m0xpd/SubHarmonics/Hardware/SubHarmonics Main Board v2.sch

## EAGLE design Hardware/SubHarmonics Main Board v2.sch (2023-10-22, an earlier design)

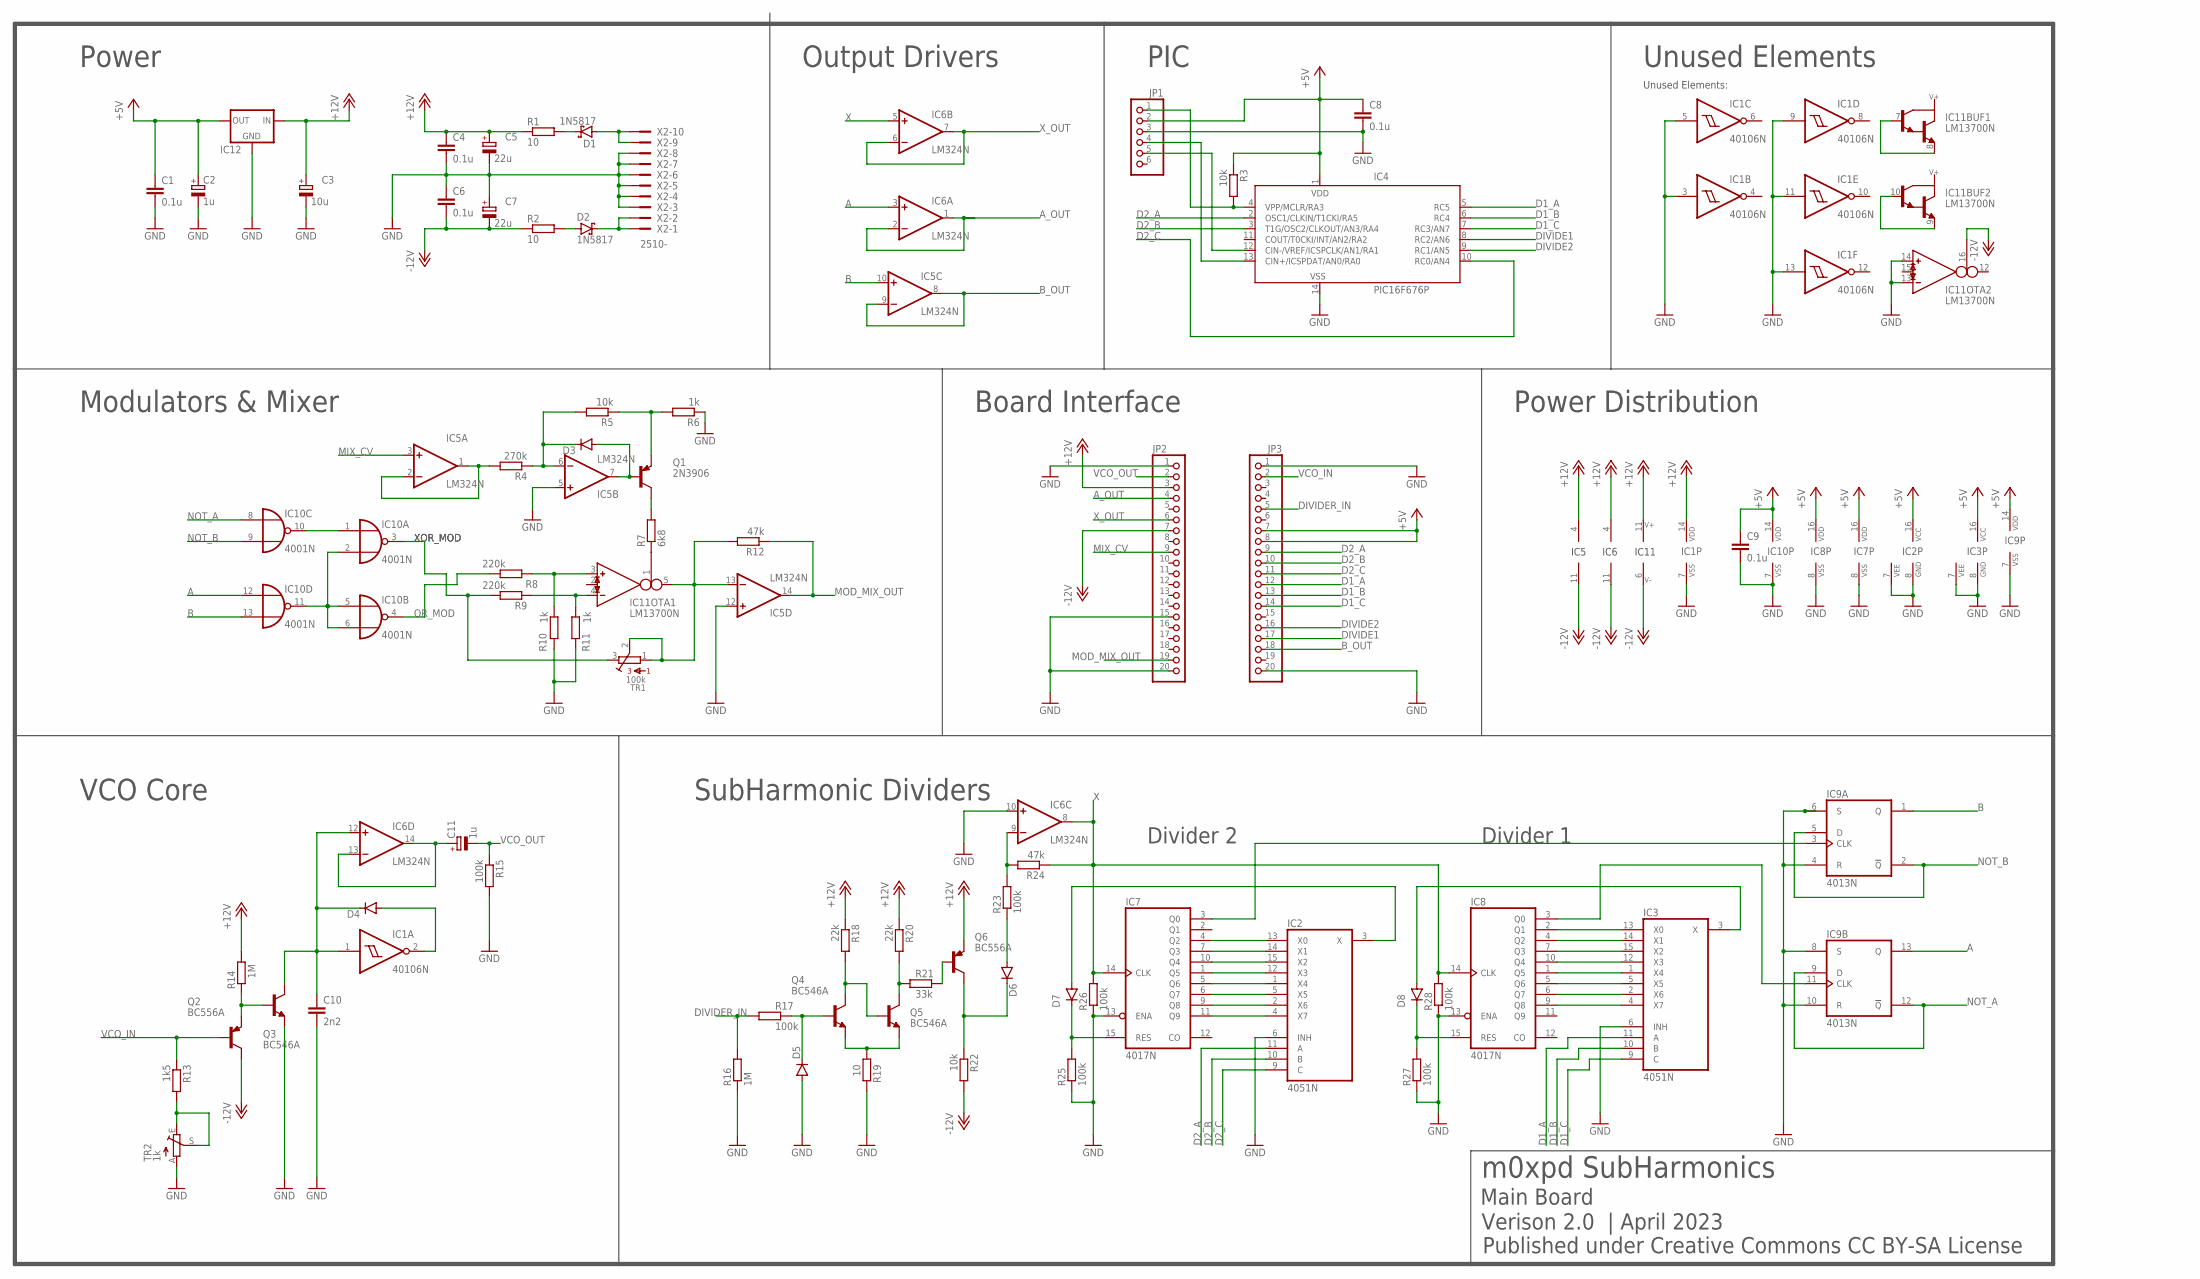
[picture p9: schematic SubHarmonics Main Board v2.sch]

Parts:
C1, C4, C6, C8, C9: 0.1u; C050-025X075
C2, C11: 1u; E2,5-5
C3: 10u; E2,5-5
C5, C7: 22u; E2,5-5
C10: 2n2; C050-030X075
D1, D2: 1N5817; DO35-7
D3, D4, D5, D6, D7, D8: 1N4148DO35-7; DO35-7
IC1: 40106N; DIL14
IC2, IC3: 4051N; DIL16
IC4: PIC16F676P; DIL14
IC5, IC6: LM324N; DIL14
IC7, IC8: 4017N; DIL16
IC9: 4013N; DIL14
IC10: 4001N; DIL14
IC11: LM13700N; DIL16
IC12: 78LXX
JP1: PINHD-1X6; 1X06
JP2, JP3: PINHD-1X20; 1X20
Q1: 2N3906; TO92
Q2, Q6: BC556A; TO92-EBC
Q3, Q4, Q5: BC546A; TO92-EBC
R1, R2, R19: 10; 0204/7
R3, R5, R22: 10k; 0204/7
R4: 270k; 0204/7
R6, R10, R11: 1k; 0204/7
R7: 6k8; 0204/7
R8, R9: 220k; 0204/7
R12, R24: 47k; 0204/7
R13: 1k5; 0204/7
R14, R16: 1M; 0204/7
R15, R17, R23, R25, R26, R27, R28: 100k; 0204/7
R18, R20: 22k; 0204/7
R21: 33k; 0204/7
TR1: 100k; BOURNS_3362P_TRIMMER
TR2: 1k; B64Y
X2: 2510-; PAK100/2500-10

Connections:
+5V: C1.1, C2.+, C8.1, C9.1, IC2.16 (VCC), IC3.16 (VCC), IC4.1 (VDD), IC7.16 (VDD), IC8.16 (VDD), IC9.14 (VDD), IC10.14 (VDD), IC12.OUT, JP1.2, JP3.7, JP3.8, R3.1
+12V: C3.+, C4.1, C5.+, IC1.14 (VDD), IC5.4 (V+), IC6.4 (V+), IC11.11 (V+), IC12.IN, JP2.3, Q6.E, R1.1, R14.2, R18.1, R20.1
-12V: C6.2, C7.-, IC5.11 (V-), IC6.11 (V-), IC11.6 (V-), IC11.16 (I_BIAS), JP2.7, Q2.C, R2.1, R22.2
A: IC6.3 (+IN), IC9.13 (Q), IC10.12 (I0)
A_OUT: IC6.1 (OUT), IC6.2 (-IN), JP2.4
B: IC5.10 (+IN), IC9.1 (Q), IC10.13 (I1)
B_OUT: IC5.8 (OUT), IC5.9 (-IN), JP3.18
D1_A: IC3.11 (A), IC4.5 (RC5), JP3.12
D1_B: IC3.10 (B), IC4.6 (RC4), JP3.13
D1_C: IC3.9 (C), IC4.7 (RC3/AN7), JP3.14
D2_A: IC2.11 (A), IC4.2 (OSC1/CLKIN/T1CKI/RA5), JP3.9
D2_B: IC2.10 (B), IC4.3 (T1G/OSC2/CLKOUT/AN3/RA4), JP3.10
D2_C: IC2.9 (C), IC4.10 (RC0/AN4), JP3.11
DIVIDE1: IC4.8 (RC2/AN6), JP3.17
DIVIDE2: IC4.9 (RC1/AN5), JP3.16
DIVIDER_IN: JP3.5, R16.2, R17.1
GND: C1.2, C2.-, C3.-, C4.2, C5.-, C6.1, C7.+, C8.2, C9.2, C10.2, D5.A, IC1.3 (I), IC1.5 (I), IC1.7 (VSS), IC1.9 (I), IC1.11 (I), IC1.13 (I), IC2.6 (INH), IC2.7 (VEE), IC2.8 (GND), IC3.6 (INH), IC3.7 (VEE), IC3.8 (GND), IC4.14 (VSS), IC5.5 (+IN), IC5.12 (+IN), IC6.10 (+IN), IC7.8 (VSS), IC7.13 (ENA), IC8.8 (VSS), IC8.13 (ENA), IC9.4 (R), IC9.6 (S), IC9.7 (VSS), IC9.8 (S), IC9.10 (R), IC10.7 (VSS), IC11.13 (IN_N), IC11.14 (IN_P), IC12.GND, JP1.3, JP2.1, JP2.15, JP2.20, JP3.1, JP3.20, Q3.E, R6.1, R10.2, R11.2, R15.2, R16.1, R19.2, R25.1, R26.1, R27.1, R28.1, TR2.A, X2.3, X2.4, X2.5, X2.6, X2.7, X2.8
MIX_CV: IC5.3 (+IN), JP2.9
MOD_MIX_OUT: IC5.14 (OUT), JP2.19, R12.1
unnamed: IC2.2 (X6), IC7.9 (Q8)
unnamed: IC5.1 (OUT), IC5.2 (-IN), R4.2
unnamed: D7.C, IC7.15 (RES), R25.2
unnamed: D7.A, IC2.3 (X)
unnamed: IC2.13 (X0), IC7.4 (Q2)
unnamed: IC2.14 (X1), IC7.7 (Q3)
unnamed: IC2.15 (X2), IC7.10 (Q4)
unnamed: IC2.12 (X3), IC7.1 (Q5)
unnamed: IC2.1 (X4), IC7.5 (Q6)
unnamed: IC2.5 (X5), IC7.6 (Q7)
unnamed: IC2.4 (X7), IC7.11 (Q9)
unnamed: IC11.3 (IN_P), R8.1, R10.1
unnamed: D1.A, X2.9, X2.10
unnamed: D1.C, R1.2
unnamed: IC4.4 (VPP/MCLR/RA3), JP1.1, R3.2
unnamed: D8.C, IC8.15 (RES), R27.2
unnamed: D8.A, IC3.3 (X)
unnamed: IC11.7 (B), IC11.8 (E)
unnamed: IC3.14 (X1), IC8.4 (Q2)
unnamed: IC3.15 (X2), IC8.7 (Q3)
unnamed: IC3.12 (X3), IC8.10 (Q4)
unnamed: IC3.1 (X4), IC8.1 (Q5)
unnamed: IC3.5 (X5), IC8.5 (Q6)
unnamed: IC3.2 (X6), IC8.6 (Q7)
unnamed: IC3.4 (X7), IC8.9 (Q8)
unnamed: IC11.4 (IN_N), R9.1, R11.1
unnamed: D2.A, R2.2
unnamed: D2.C, X2.1, X2.2
unnamed: IC11.9 (E), IC11.10 (B)
unnamed: IC11.1 (I_BIAS), R7.1
unnamed: IC4.13 (CIN+/ICSPDAT/AN0/RA0), JP1.4
unnamed: IC4.12 (CIN-/VREF/ICSPCLK/AN1/RA1), JP1.5
unnamed: IC3.13 (X0), IC8.2 (Q1)
unnamed: IC8.3 (Q0), IC9.11 (CLK)
unnamed: IC7.3 (Q0), IC9.3 (CLK)
unnamed: R13.2, TR2.E, TR2.S
unnamed: D6.C, Q6.C, R22.1
unnamed: D6.A, R23.1
unnamed: D4.A, IC1.2 (O)
unnamed: C10.1, D4.C, IC1.1 (I), IC6.12 (+IN), Q3.C
unnamed: Q2.E, Q3.B, R14.1
unnamed: IC6.9 (-IN), R23.2, R24.2
unnamed: C11.+, IC6.13 (-IN), IC6.14 (OUT)
unnamed: Q4.E, Q5.E, R19.1
unnamed: IC10.1 (I0), IC10.10 (O)
unnamed: IC10.2 (I1), IC10.5 (I0), IC10.6 (I1), IC10.11 (O)
unnamed: D5.C, Q4.B, R17.2
unnamed: Q1.1 (C), R7.2
unnamed: D3.C, IC5.6 (-IN), R4.1, R5.2
unnamed: Q4.C, Q5.B, R18.2
unnamed: Q5.C, R20.2, R21.1
unnamed: D3.A, IC5.7 (OUT), Q1.2 (B)
unnamed: Q1.3 (E), R5.1, R6.2
unnamed: Q6.B, R21.2
unnamed: IC5.13 (-IN), IC11.5 (OUT), R12.2, TR1.1, TR1.2
NOT_A: IC9.9 (D), IC9.12 (!Q), IC10.8 (I0)
NOT_B: IC9.2 (!Q), IC9.5 (D), IC10.9 (I1)
OR_MOD: IC10.4 (O), R8.2
VCO_IN: JP3.2, Q2.B, R13.1
VCO_OUT: C11.-, JP2.2, R15.1
X: IC6.5 (+IN), IC6.8 (OUT), IC7.14 (CLK), IC8.14 (CLK), R24.1, R26.2, R28.2
XOR_MOD: IC10.3 (O), R9.2, TR1.3
X_OUT: IC6.6 (-IN), IC6.7 (OUT), JP2.6

Notes on the sheet:
Unused Elements:
Divider 1
Divider 2
m0xpd SubHarmonics
Main Board
Verison 2.0 | April 2023
Published under Creative Commons CC BY-SA License
VCO Core
SubHarmonic Dividers
Modulators & Mixer
Power
Output Drivers
PIC
Unused Elements
Power Distribution
Board Interface
IC5
IC6
IC11
